hsiadd/Turtle-Backpack/Enclosure Designs/TOS V1/tos_top_1.png

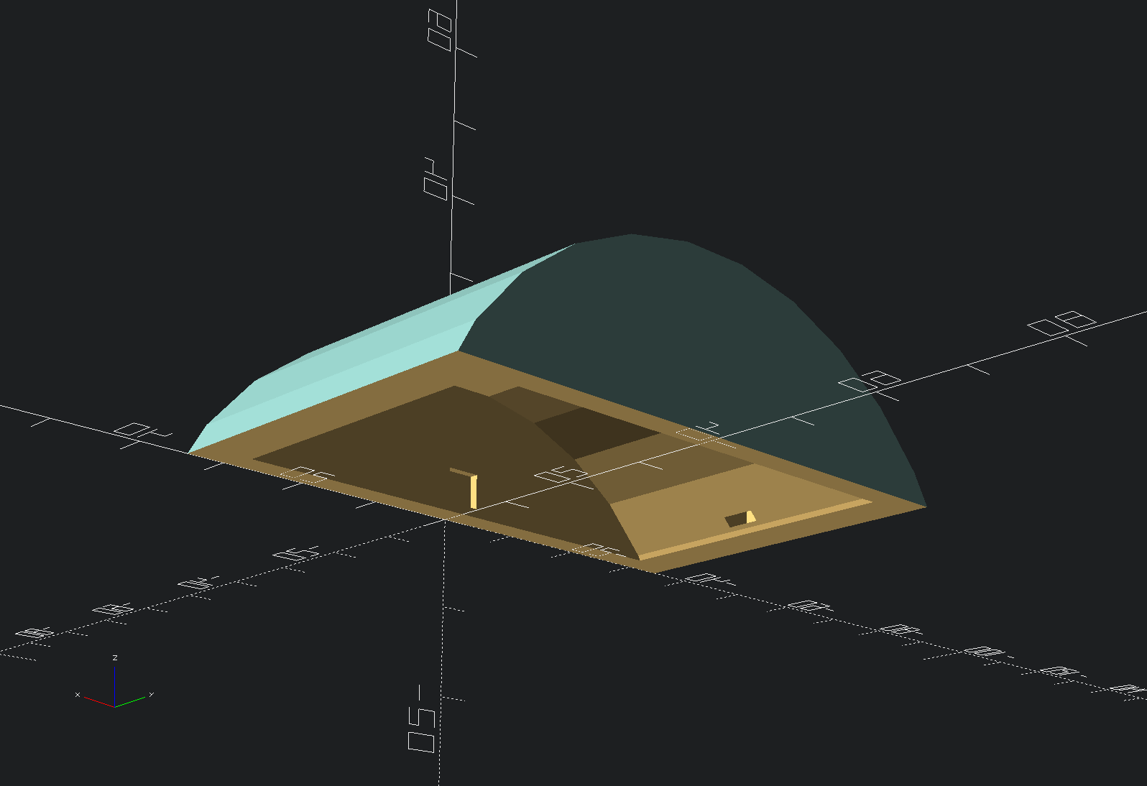
Enclosure Designs/TOS V1/tos_top_1.png
