hsiadd/Turtle-Backpack/Source Code/Enclosures/TNG/tos_top_2.scad

/*
    TOS Version 2 Top
    

*/
rotate(a=[270,0,0]) {
    translate([0,20, 0]) {
        difference() {
            // Main Body Outside
            difference() {
                cylinder(h=41, r=40);
                translate([0,30,0]) {
                    cube(99, center=true);
                }
                
            };

            // Main Body Inside
            difference() {
          
                translate([0,0,2]) {
                    cylinder(h=37, r=35);
                };        
                translate([0,30,0]) {
                    cube(99, center=true);
                }

            };
            
            // Inside Recesses
            // Front and back
             translate([29,-22.5,20]) {
                cube(4, center=true);
            }
            
            translate([-29,-22.5,20]) {
                cube(4, center=true);
            }
          /*  
            // Left and right
            translate([0,-23,37]) {
                cube(4, center=true);
            }
                
            translate([0,-23,4]) {
                cube(4, center=true);
            }
            */
        }
    }
}
